ELE795-A2017-07/ele795-A2017-07/Electronics/POWER/AlimModel.png

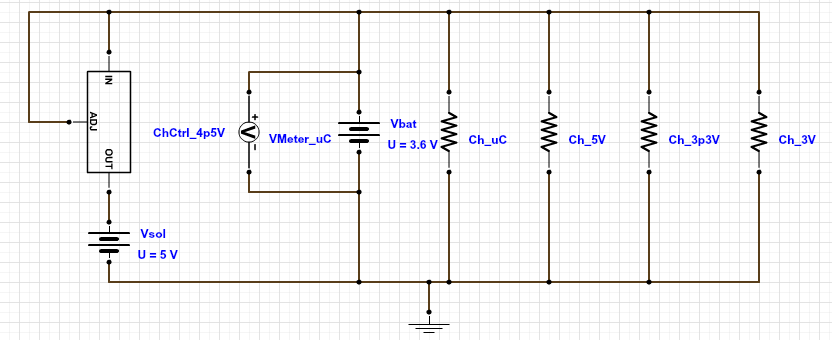
Electronics/POWER/AlimModel.png
