ELE795-A2017-07/ele795-A2017-07/Electronics/SENSOR_UNIT/arduino_micro_footprint.png

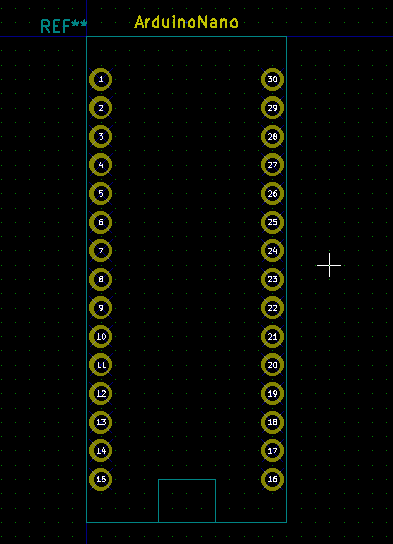
Electronics/SENSOR_UNIT/arduino_micro_footprint.png
