ELE795-A2017-07/ele795-A2017-07/Electronics/SENSOR_UNIT/pcb_layout.png

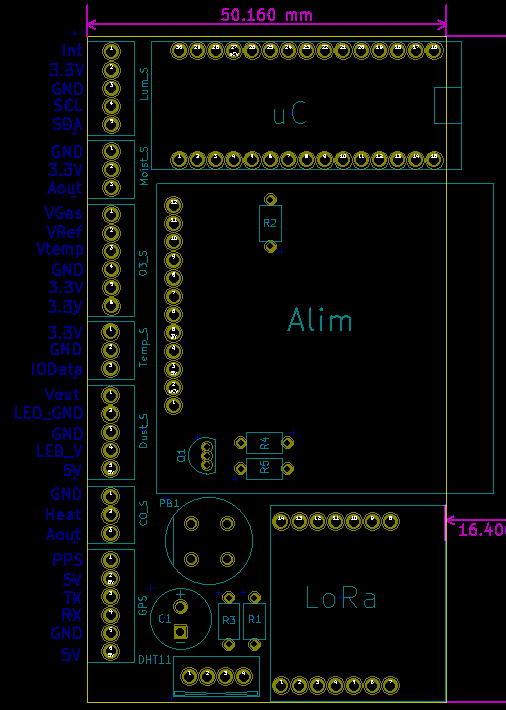
Electronics/SENSOR_UNIT/pcb_layout.png
