ELE795-A2017-07/ele795-A2017-07/Electronics/POWER/reg_step_down_3p3V.png

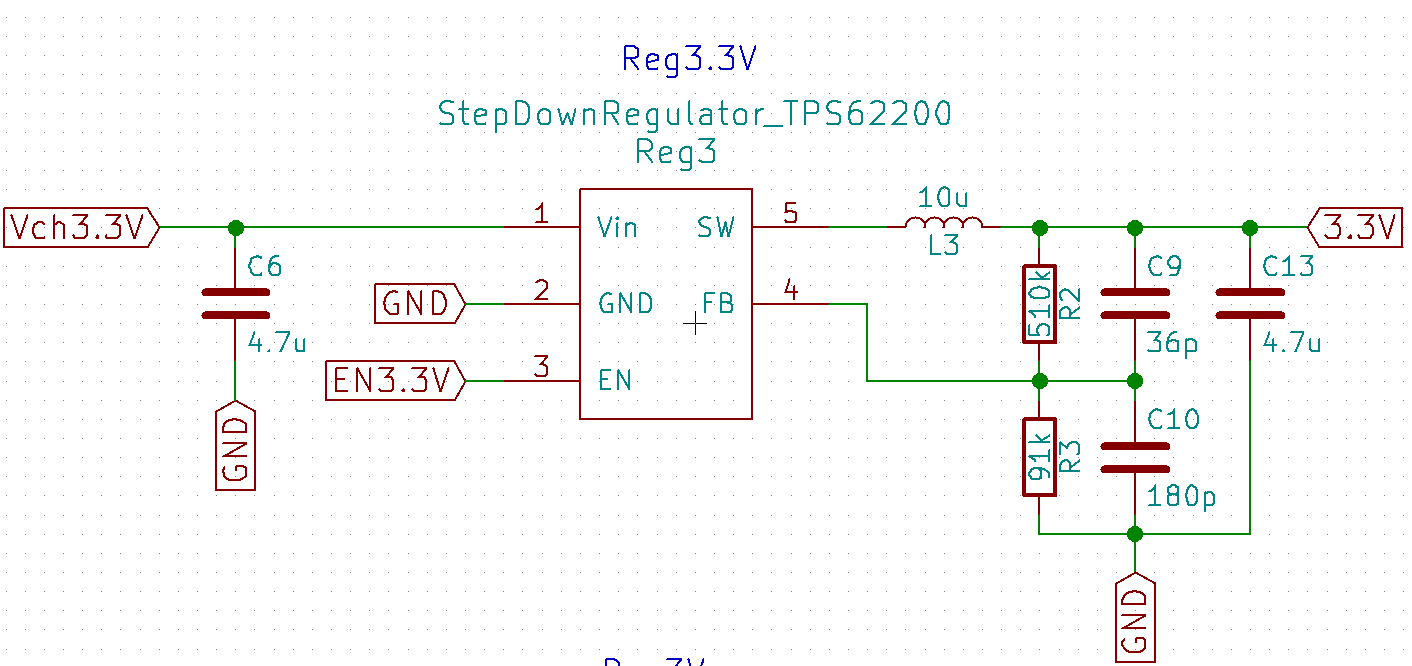
Electronics/POWER/reg_step_down_3p3V.png
