ELE795-A2017-07/ele795-A2017-07/Electronics/POWER/reg_step_up.png

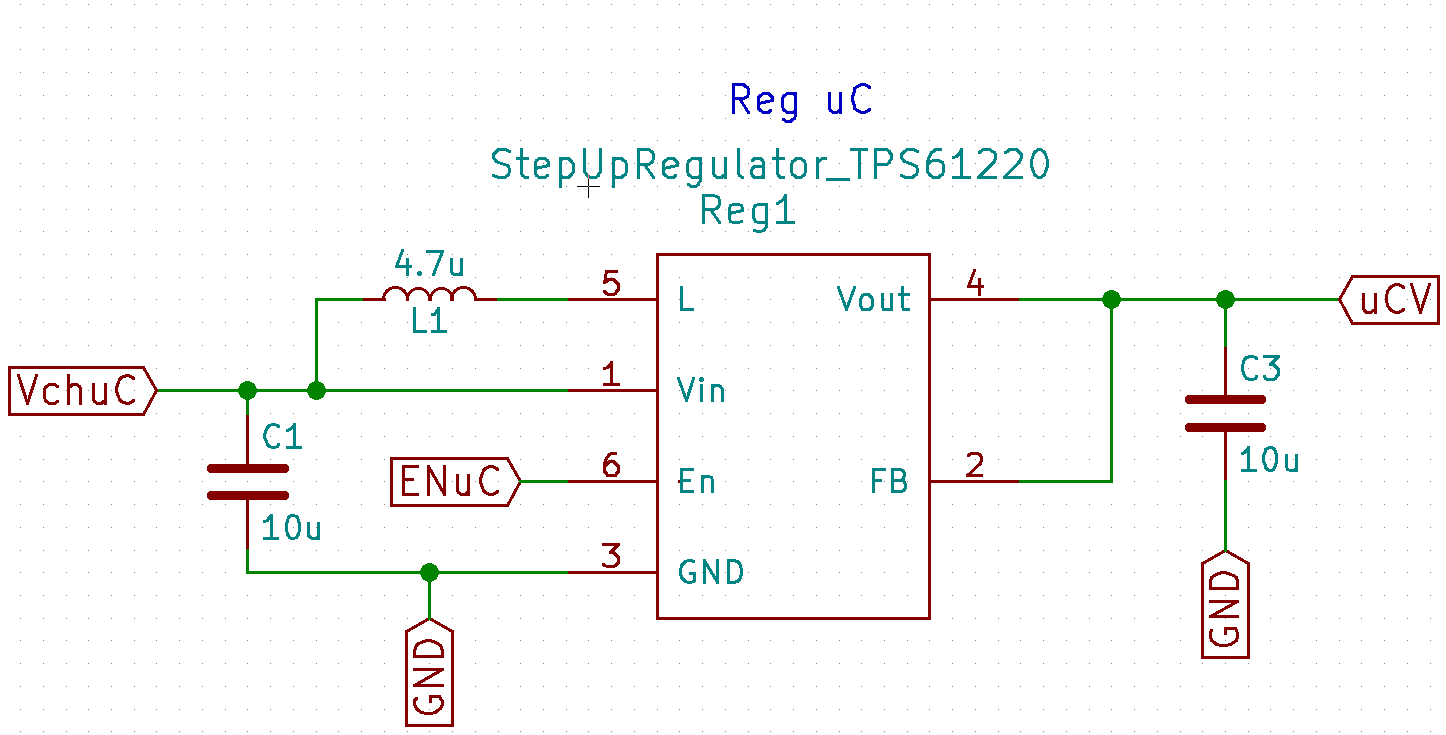
Electronics/POWER/reg_step_up.png
